gerb-ster/MiniMoog-VCF/images/IMG_3971.jpeg

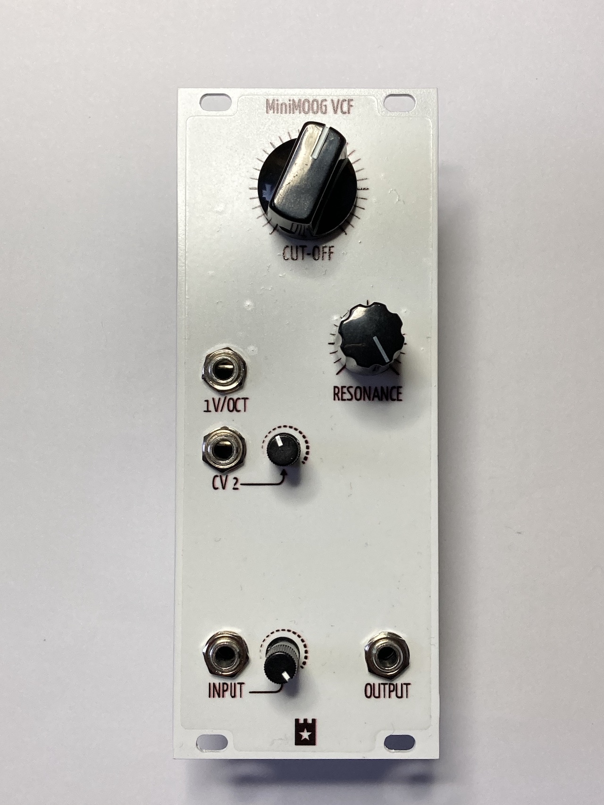
images/IMG_3971.jpeg
