gerb-ster/MiniMoog-VCF/images/IMG_3973.jpeg

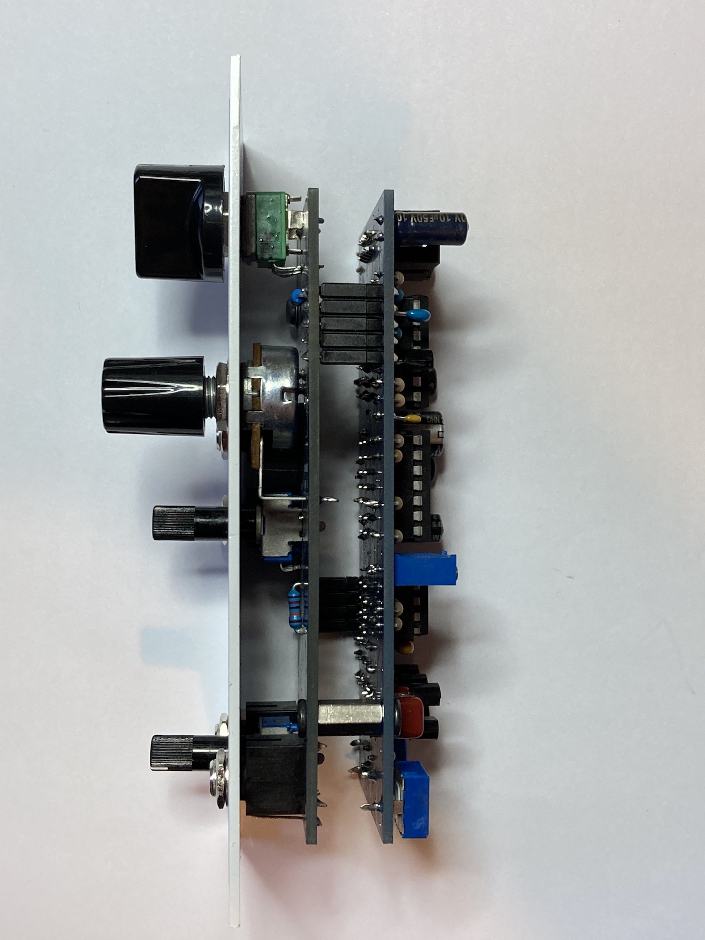
images/IMG_3973.jpeg
