gerb-ster/MiniMoog-VCF/images/IMG_3974.jpeg

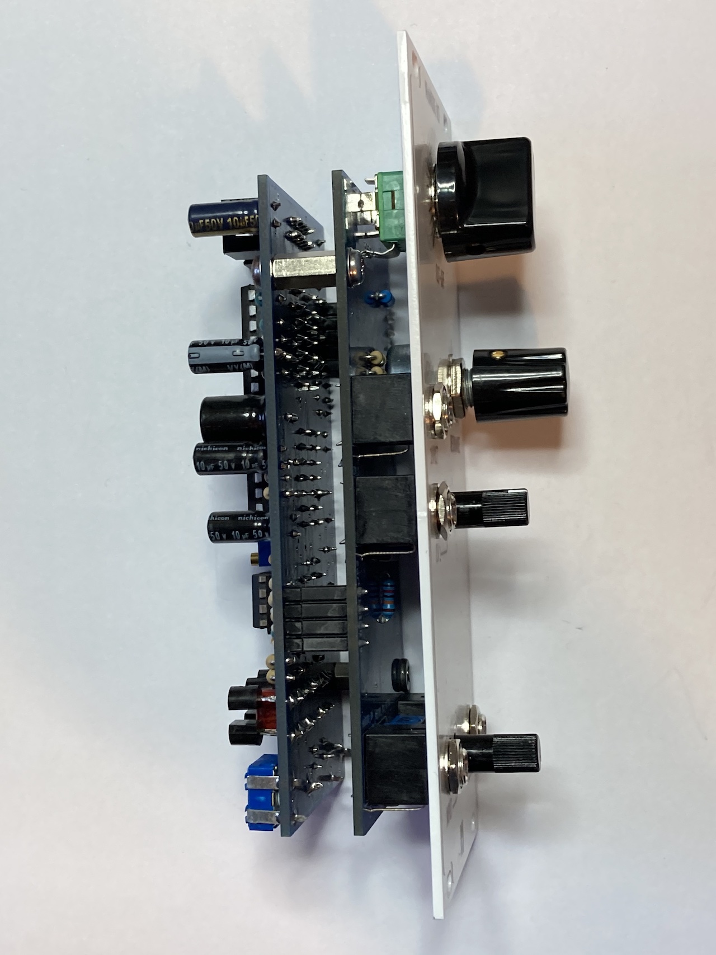
images/IMG_3974.jpeg
