gerb-ster/MiniMoog-VCF/images/IMG_3975.jpeg

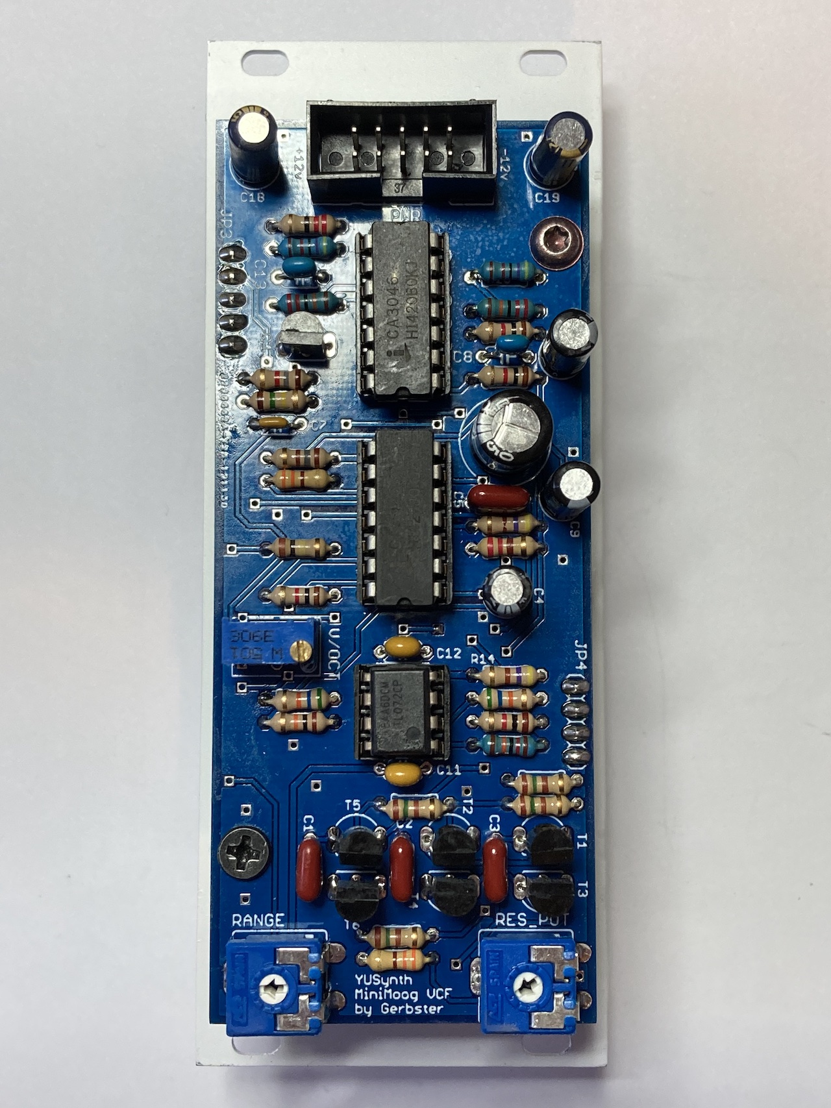
images/IMG_3975.jpeg
