gerb-ster/MiniMoog-VCF/images/IMG_3976.jpeg

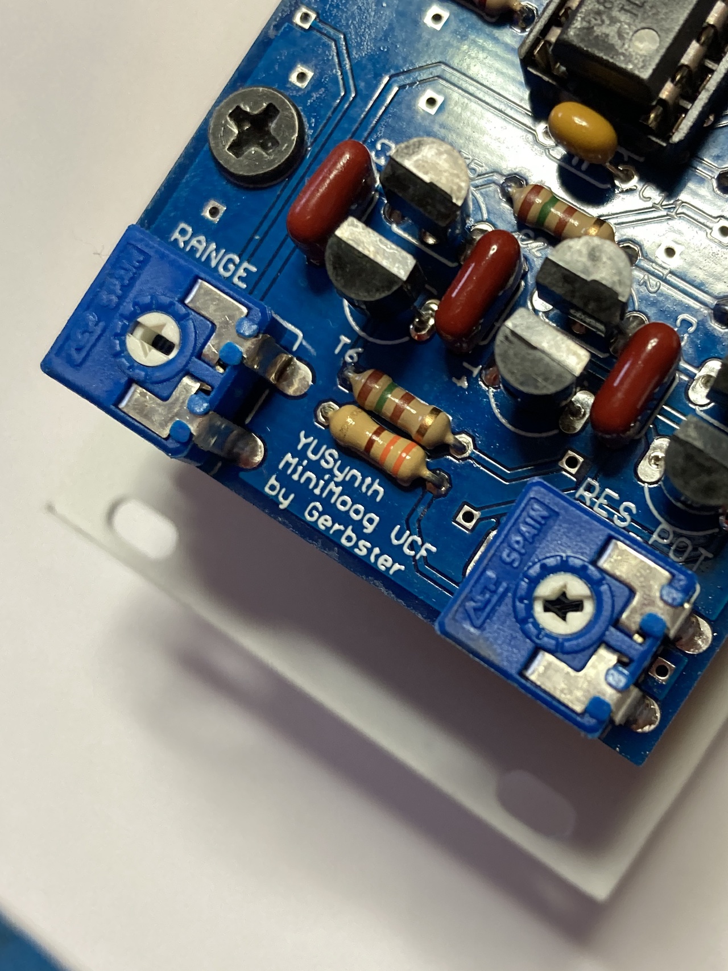
images/IMG_3976.jpeg
