gerb-ster/MiniMoog-VCF/images/IMG_3996.jpeg

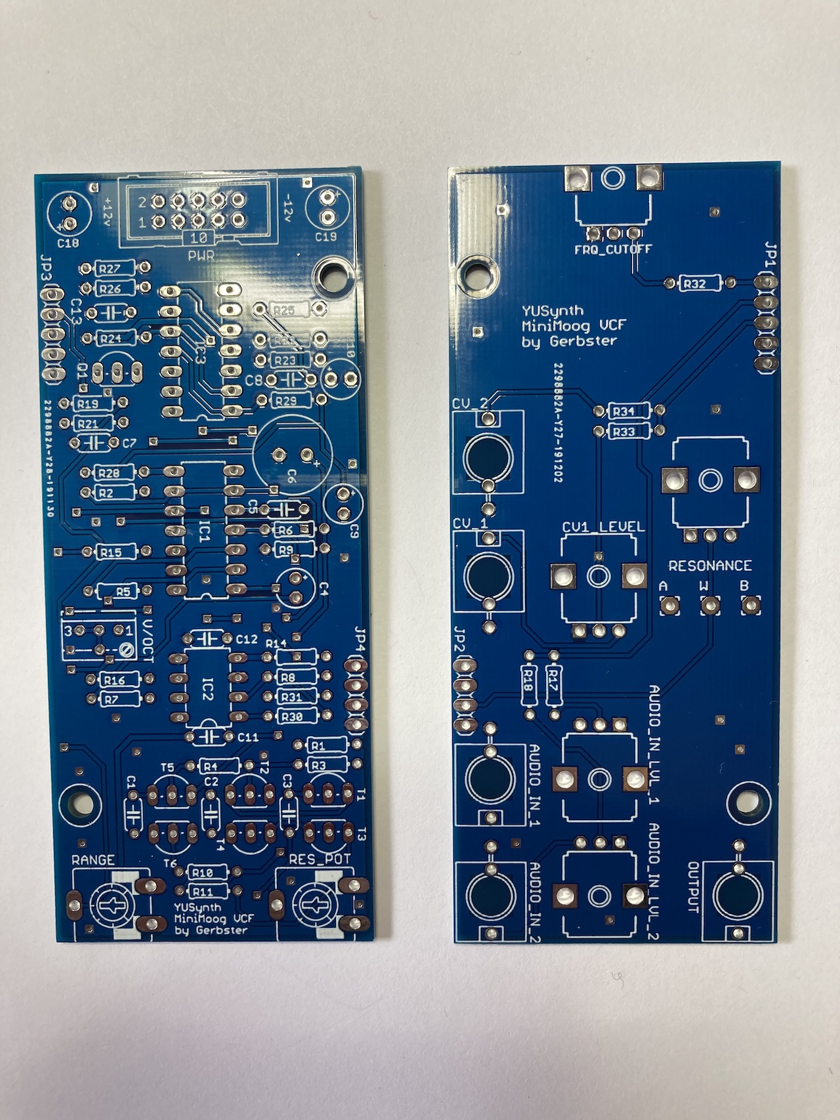
images/IMG_3996.jpeg
